nonik0/Light-Rail/images/github-qr.png

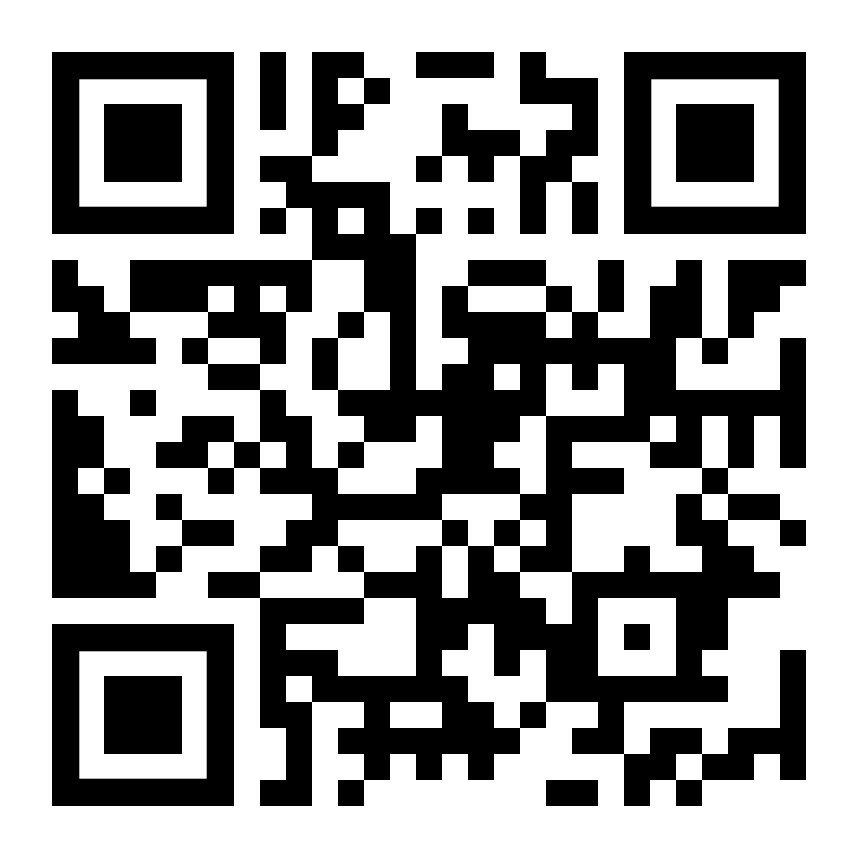
images/github-qr.png
