nonik0/Light-Rail/images/train_drawing_1.png

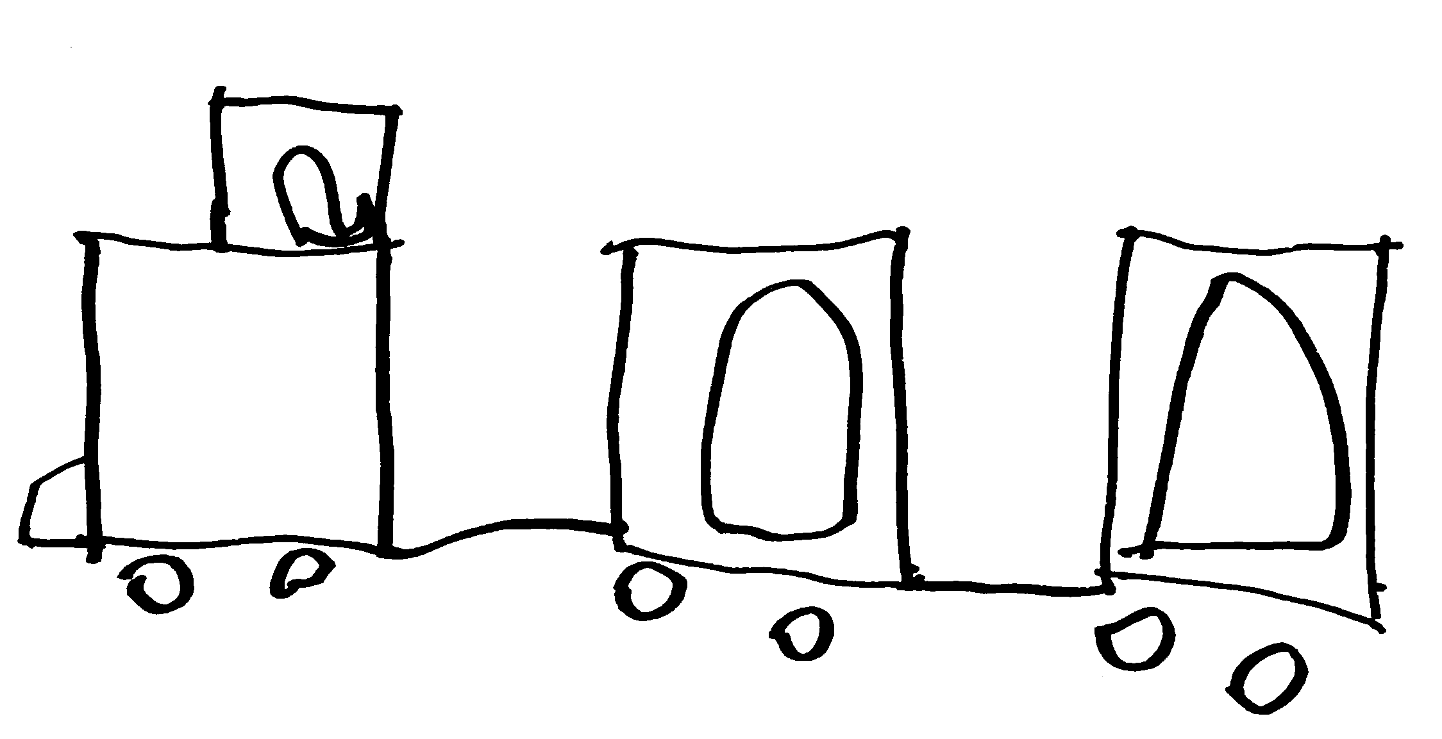
images/train_drawing_1.png
