nonik0/Light-Rail/images/train_drawing_2.png

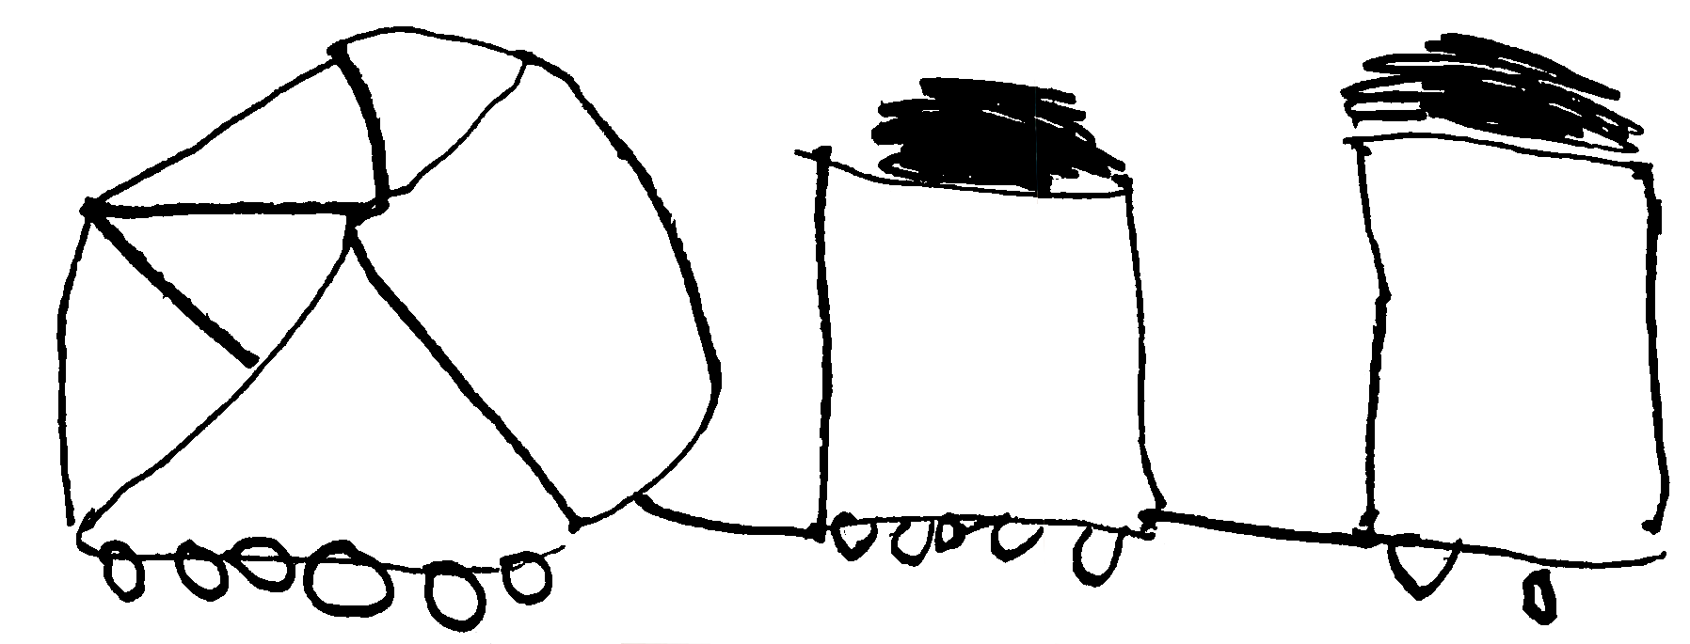
images/train_drawing_2.png
