nonik0/Light-Rail/firmware/rust/src/game_state.rs

use heapless::Vec;

use crate::{
    cargo::*,
    game_settings::GameSettings,
    location::{Direction, NUM_PLATFORMS, NUM_SWITCHES},
    platform::Platform,
    random::Rand,
    switch::Switch,
    train::{Car, Train, DEFAULT_SPEED},
    NUM_DIGITS,
};

pub const MAX_CARS: usize = 128;
pub const MAX_TRAINS: usize = 8;
pub const TRAIN_SIZE: usize = MAX_CARS / MAX_TRAINS;

#[derive(Clone, Copy, PartialEq)]
pub enum DisplayState {
    None,
    Score(u16),
    Segments([u8; NUM_DIGITS as usize]),
    Text([u8; NUM_DIGITS as usize]),
}

#[allow(dead_code)]
impl DisplayState {
    pub const DED: DisplayState = DisplayState::Text(*b"ded");
    pub const GG: DisplayState = DisplayState::Text(*b" gg");
    pub const OVR: DisplayState = DisplayState::Text(*b"ovr");
    pub const PAUSE_BYTES: [u8; NUM_DIGITS as usize] = [0u8, 0x36, 0u8];
    pub const PAUSE: DisplayState = DisplayState::Segments(Self::PAUSE_BYTES);
}

// TODO: move mutable stuff to methods and make stuff private?
pub struct GameState {
    pub target_mode_index: usize, // in state so menu mode can manipulate it
    // TODO: combine active/over/paused into single enum state
    pub is_over: bool,   // stops entity updates, game is over
    pub is_paused: bool, // stops entity updates, game is still active
    pub redraw: bool,    // flag to redraw board LEDs
    pub display: DisplayState,
    pub settings: GameSettings,

    // game entities
    pub cars: [Car; MAX_CARS],
    pub trains: Vec<Train, MAX_TRAINS>,
    pub platforms: [Platform; NUM_PLATFORMS],
    pub switches: [Switch; NUM_SWITCHES],
}

impl GameState {
    pub fn add_train(&mut self, cargo: Cargo, num_cars: u8, max_cars: u8, speed: Option<u8>) {
        if self.trains.is_full() {
            return;
        }

        // TODO: for now, simple allocation method that divides evenly on MAX_TRAINS, only snake allocated single train with max cars
        let cars_ptr = unsafe { self.cars.as_mut_ptr().add(self.trains.len() * TRAIN_SIZE) };
        let loc = self.rand_platform().track_location();
        let mut train = Train::new(cars_ptr, max_cars, loc, cargo, speed);
        for _ in 1..num_cars {
            train.add_car(cargo);
        }
        self.trains.push(train).ok();
        self.redraw = true;
    }

    #[allow(dead_code)]
    pub fn remove_train(&mut self) {
        if self.trains.len() > 1 {
            self.trains.pop();
            self.redraw = true;
        }
    }

    /// Initializes the game state with a single train with given parameters.
    pub fn init_trains(&mut self, cargo: Cargo, num_cars: u8, max_cars: u8) {
        // init first train
        if self.trains.len() > 0 {
            while self.trains.len() > 1 {
                self.trains.pop();
            }

            // reuse existing train for smooth transition between modes
            let train = &mut self.trains[0];
            train.init_cars(cargo, num_cars, max_cars);
            train.set_speed(DEFAULT_SPEED);
            self.redraw = true;
        } else {
            self.add_train(cargo, num_cars, max_cars, None);
        }
    }

    pub fn init_platforms(&mut self, cargo: Cargo) {
        for platform in self.platforms.iter_mut() {
            if !platform.is_empty() {
                platform.set_cargo_out(cargo);
                platform.set_phase_speed(1);
            }
        }
    }

    pub fn clear_platforms(&mut self) {
        for platform in self.platforms.iter_mut() {
            platform.clear_cargo();
        }
    }

    pub fn rand_platform(&self) -> &Platform {
        let rand_platform_index = Rand::from_range(0, self.platforms.len() as u8 - 1) as usize;
        &self.platforms[rand_platform_index]
    }

    // Helper/utility functions for state

    /// If the train just left a switch, switch it.
    pub fn train_switch(&mut self, train_index: usize) {
        let train = &self.trains[train_index];
        let caboose_loc = train.caboose().loc;
        let last_loc = train.last_loc();

        // If train just left a switch, randomly switch it
        for switch in self.switches.iter_mut() {
            if caboose_loc == switch.location() {
                continue; // Train is entering, not leaving
            }
            for dir in [Direction::Anode, Direction::Cathode] {
                if switch.active_location(dir) == Some(last_loc) {
                    switch.switch();
                    break;
                }
            }
        }
    }

    /// True if the train can actually transfer with a given platform: either the
    /// platform wants cargo the train is carrying, or the platform is offering
    /// cargo and the train has room to take it.
    #[inline(always)]
    fn platform_transfer_possible(train: &Train, platform: &Platform) -> bool {
        if platform.is_empty() {
            return false;
        }

        let (platform_cargo, is_receiving) = platform.cargo();
        if is_receiving {
            train.has_cargo(platform_cargo)
        } else {
            !train.is_full()
        }
    }

    // True if train is within `steps` advances of a platform that has cargo the
    // train is actually able to pick up or drop off
    pub fn train_approaching_platform(&self, train_index: usize, steps: u8) -> bool {
        let train = &self.trains[train_index];
        let mut loc = train.front();
        let mut dir = train.direction();

        for _ in 0..steps {
            let is_switched = self
                .switches
                .iter()
                .any(|switch| loc == switch.location() && switch.is_switched(dir));
            let (next_loc, next_dir) = loc.next(dir, is_switched);
            loc = next_loc;
            dir = next_dir;
        }

        self.platforms.iter().any(|platform| {
            platform.track_location() == loc && Self::platform_transfer_possible(train, platform)
        })
    }

    /// True if a train's engine is at the last platform track, i.e. the train is fully "in position"
    /// in front of a set of adjacent platforms, and the train has cargo to pick up or drop off
    pub fn train_ready_at_platform(&self, train_index: usize) -> bool {
        let train = &self.trains[train_index];
        let engine_loc = train.front();
        let next_loc = train.next_loc(&self.switches);

        let mut engine_at_platform = false;
        let mut next_loc_at_platform = false;
        let mut any_ready = false;

        for platform in self.platforms.iter() {
            let loc = platform.track_location();

            if loc == engine_loc {
                engine_at_platform = true;
            }
            if loc == next_loc {
                next_loc_at_platform = true;
            }
            if train.at_location(loc) && Self::platform_transfer_possible(train, platform) {
                any_ready = true;
            }
        }

        engine_at_platform && !next_loc_at_platform && any_ready
    }
}
