nonik0/Light-Rail/firmware/rust/src/train.rs

use random_trait::Random;

use crate::{
    cargo::*,
    game_settings::GameSettings,
    location::{Direction, Location},
    random::Rand,
    switch::Switch,
};

pub const DEFAULT_SPEED: u8 = 10;
const MIN_SPEED: u8 = 0;
const MAX_SPEED: u8 = 100;

#[derive(Clone, Copy, Default)]
pub struct Car {
    pub loc: Location,
    pub cargo: Cargo,
    pub last_brightness: u8,
}

pub struct Train {
    direction: Direction,
    speed: u8,
    speed_counter: u8,
    cars_ptr: *mut Car,
    num_cars: u8,
    max_cars: u8,
    last_loc: Location,
    phase: u8, // phase of the train, used for PWM
}

impl Train {
    pub fn new(
        cars_ptr: *mut Car,
        max_cars: u8,
        loc: Location,
        cargo: Cargo,
        speed: Option<u8>,
    ) -> Self {
        let mut new_self = Self {
            direction: if Rand::default().get_bool() {
                Direction::Anode
            } else {
                Direction::Cathode
            },
            speed: speed.unwrap_or(DEFAULT_SPEED),
            speed_counter: 0,
            cars_ptr,
            num_cars: 0,
            max_cars,
            last_loc: loc,
            phase: Rand::default().get_u8(), // initial phase
        };

        new_self.add_car(cargo);
        new_self
    }

    pub fn add_car(&mut self, cargo: Cargo) -> Option<Location> {
        if self.num_cars >= self.max_cars {
            return None;
        }

        let loc = if self.num_cars == 0 {
            self.last_loc
        } else {
            let caboose_loc = self.caboose().loc;
            let inv_caboose_dir = if self.num_cars > 1 {
                let next_car_loc = self.cars()[self.num_cars as usize - 2].loc;
                if caboose_loc
                    .next(Direction::Anode, Rand::default().get_bool())
                    .0
                    == next_car_loc
                {
                    Direction::Cathode
                } else {
                    Direction::Anode
                }
            } else {
                self.direction
            };
            caboose_loc.next(inv_caboose_dir, false).0 // TODO: is switched
        };

        self.num_cars += 1;
        let new_car = self.cars_mut().last_mut().unwrap();
        new_car.loc = loc;
        new_car.cargo = cargo;

        Some(loc)
    }

    #[allow(dead_code)]
    pub fn remove_car(&mut self) -> Option<Location> {
        if self.num_cars <= 1 {
            return None;
        }

        let loc = self.caboose().loc;
        self.num_cars -= 1;
        Some(loc)
    }

    /// Unsafe function if not called properly, should only be called when first train is initialized
    pub fn init_cars(&mut self, cargo: Cargo, num_cars: u8, max_cars: u8) {
        self.num_cars = num_cars;
        self.max_cars = max_cars;

        for car in self.cars_mut().iter_mut() {
            car.cargo = cargo;
            car.last_brightness = 0;
        }
    }

    // Game tick for train during game over or pause, to keep led updates occuring
    pub fn update<F>(
        &mut self,
        settings: &GameSettings,
        mut update_callback: F,
        force_update: bool,
    )
    where
        F: FnMut(Location, u8),
    {
        self.phase = self.phase.wrapping_add(1);

        for car in self.cars_mut().iter_mut() {
            let brightness = car
                .cargo
                .car_brightness(self.phase, settings.car_brightness());
            if force_update || car.last_brightness != brightness {
                car.last_brightness = brightness;
                update_callback(car.loc, brightness);
            }
        }
    }

    /// Game tick for train, returns location updates as cars move along track
    pub fn advance<F>(
        &mut self,
        settings: &GameSettings,
        switches: &[Switch],
        mut update_callback: F,
        force_update: bool,
    ) -> bool
    where
        F: FnMut(Location, u8),
    {
        self.speed_counter += self.speed;

        // If not enough speed accumulated, just update brightness and return
        if self.speed_counter < MAX_SPEED {
            self.update(settings, update_callback, force_update);
            return false;
        }

        self.phase = self.phase.wrapping_add(1);
        self.speed_counter -= MAX_SPEED;

        // Move train cars from rear to front, updating locations and brightness
        self.last_loc = self.caboose().loc;
        update_callback(self.last_loc, 0);

        let cars = self.cars_mut();
        for i in (1..cars.len()).rev() {
            cars[i].loc = cars[i - 1].loc;
            let brightness = cars[i]
                .cargo
                .car_brightness(self.phase, settings.car_brightness());
            update_callback(cars[i].loc, brightness);
        }

        // Advance the engine to the next location and update brightness
        let (next_loc, new_dir) = self.next(switches);
        self.engine_mut().loc = next_loc;
        self.direction = new_dir;
        let brightness = self
            .engine()
            .cargo
            .car_brightness(self.phase, settings.car_brightness());
        update_callback(self.front(), brightness);

        true
    }

    // Returns the train engine's next location
    pub fn next_loc(&self, switches: &[Switch]) -> Location {
        let (loc, _) = self.next(switches);
        loc
    }

    /// Returns the train engine's next location and direction
    pub fn next(&self, switches: &[Switch]) -> (Location, Direction) {
        // Determine if the front of the train is on a switched track
        let front_loc = self.front();
        let is_switched = switches
            .iter()
            .any(|switch| front_loc == switch.location() && switch.is_switched(self.direction));

        // Get next location and direction
        self.front().next(self.direction, is_switched)
    }

    /// Returns the vector of cars in the train
    pub fn cars(&self) -> &[Car] {
        unsafe { core::slice::from_raw_parts(self.cars_ptr, self.num_cars as usize) }
    }

    /// Returns the number of cars in the train
    pub fn len(&self) -> usize {
        self.num_cars as usize
    }

    /// Returns speed of the train
    pub fn speed(&self) -> u8 {
        self.speed
    }

    /// Sets the speed of the train, clamping it between MIN_SPEED and MAX_SPEED
    pub fn set_speed(&mut self, speed: u8) {
        self.speed = speed.clamp(MIN_SPEED, MAX_SPEED);
        self.speed_counter = 0;
    }

    /// Advances speed counter so train advances next tick
    pub fn force_advance_next_tick(&mut self) {
        self.speed_counter = MAX_SPEED;
    }

    // Returns true if the train has a car with cargo
    pub fn has_cargo(&self, cargo: Cargo) -> bool {
        self.cars().iter().any(|car| car.cargo == cargo)
    }

    /// Returns true if every car is currently carrying cargo
    pub fn is_full(&self) -> bool {
        self.cars().iter().all(|car| car.cargo != Cargo::Empty)
    }

    /// Adds cargo to train, returns true if train loads cargo into an available empty car
    /// TODO: add location so cargo can be added to nearest empty car?
    pub fn load_cargo(&mut self, cargo: Cargo) -> bool {
        match self.cars_mut().iter_mut().find(|car| car.cargo == Cargo::Empty) {
            Some(car) => {
                car.cargo = cargo;
                true
            }
            None => false,
        }
    }

    /// Unloads cargo from the train, returns true if train removes cargo from a car that has it
    pub fn unload_cargo(&mut self, cargo: Cargo) -> bool {
        match self.cars_mut().iter_mut().find(|car| car.cargo == cargo) {
            Some(car) => {
                car.cargo = Cargo::Empty;
                true
            }
            None => false,
        }
    }


    /// Returns reference to the first car of the train (engine)
    pub fn engine(&self) -> &Car {
        self.cars().first().unwrap()
    }

    /// Returns the current location of the train engine
    pub fn front(&self) -> Location {
        self.engine().loc
    }

    /// Returns reference to the last car of the train (caboose)
    pub fn caboose(&self) -> &Car {
        self.cars().last().unwrap()
    }

    /// Returns the direction of the train
    pub fn direction(&self) -> Direction {
        self.direction
    }

    /// Returns the previous location of the caboose before the last move
    pub fn last_loc(&self) -> Location {
        self.last_loc
    }

    /// Returns bool if any car is at the given location
    pub fn at_location(&self, loc: Location) -> bool {
        self.cars().iter().any(|car| car.loc == loc)
    }

    // private mutable functions

    /// Returns mutable reference to the engine (first car of the train)
    fn engine_mut(&mut self) -> &mut Car {
        self.cars_mut().first_mut().unwrap()
    }

    // /// Returns mutable reference to the last car of the train (caboose)
    // fn caboose_mut(&mut self) -> &mut Car {
    //     self.cars_mut().last_mut().unwrap()
    // }

    /// Returns the vector of cars in the train
    fn cars_mut(&self) -> &mut [Car] {
        unsafe { core::slice::from_raw_parts_mut(self.cars_ptr, self.num_cars as usize) }
    }
}

impl core::ops::Index<usize> for Train {
    type Output = Car;

    fn index(&self, index: usize) -> &Self::Output {
        &self.cars()[index]
    }
}
