nonik0/Light-Rail/firmware/cpp/track.h

#pragma once

#include <Arduino.h>

#define TRACK_COUNT 144
#define TRACK_NONE 0xFF

struct Track
{
  // defined "backwards" because AVR is little-endian
  uint8_t cathodeNextLoc2; // neighbor2 on cathode side
  uint8_t anodeNextLoc2;   // neighbor2 on anode side
  uint8_t cathodeNextLoc;  // neighbor on cathode side
  uint8_t anodeNextLoc;    // neighbor on anode side
};

#ifndef LED_BACKPACK_MATRIX
const uint32_t TrackData[TRACK_COUNT] = {
    0x6111FFFF, // track 0/0x00
    0x20202020, // track 1/0x01 PLATFORM
    0x3003FFFF, // track 2/0x02
    0x7002FFFF, // track 3/0x03
    0x5082FFFF, // track 4/0x04
    0x60606060, // track 5/0x05 PLATFORM
    0x70707070, // track 6/0x06 PLATFORM
    0x8042FFFF, // track 7/0x07
    0x0D69FF1D, // track 8/0x08
    0x682DFFFF, // track 9/0x09
    0x4838FFFF, // track 10/0x0A
    0x3B5CFFFF, // track 11/0x0B
    0x1839FFFF, // track 12/0x0C
    0x0868FFFF, // track 13/0x0D
    0x4C4EFFFF, // track 14/0x0E
    0x88888888, // track 15/0x0F PLATFORM
    0x4920FFFF, // track 16/0x10
    0x0021FFFF, // track 17/0x11
    0x2933FFFF, // track 18/0x12
    0x53535353, // track 19/0x13 PLATFORM
    0x5154FFFF, // track 20/0x14
    0x61616161, // track 21/0x15 PLATFORM
    0x5351FFFF, // track 22/0x16
    0x1E81FFFF, // track 23/0x17
    0x4F0CFFFF, // track 24/0x18
    0x594AFFFF, // track 25/0x19
    0x39393939, // track 26/0x1A PLATFORM
    0x6949FFFF, // track 27/0x1B
    0x59595959, // track 28/0x1C PLATFORM
    0x0848FFFF, // track 29/0x1D
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
    0x8789FFFF, // track 136/0x88
    0x888AFFFF, // track 137/0x89
    0x898BFFFF, // track 138/0x8A
    0x8A8CFFFF, // track 139/0x8B
    0x8B8DFFFF, // track 140/0x8C
    0x8C8EFFFF, // track 141/0x8D
    0x8D8FFFFF, // track 142/0x8E
    0x8E7FFFFF, // track 143/0x8F
};
#endif
