nonik0/Light-Rail/firmware/rust/src/game.rs

use as1115::AS1115;
use embedded_hal::i2c::I2c;
use heapless::Vec;
use is31fl3731::{gamma, IS31FL3731};

use crate::{
    game_settings::GameSettings,
    game_state::*,
    input::{BoardInput, InputDirection, InputEvent},
    location::Location,
    modes::*,
    platform::Platform,
    switch::Switch,
    tone::TimerTone,
    train::{Car, Train},
    NUM_DIGITS,
};

pub struct Game<I2C>
where
    I2C: I2c,
{
    // board components
    board_buzzer: TimerTone,
    board_digits: AS1115<I2C, NUM_DIGITS>,
    board_input: BoardInput,
    board_leds: IS31FL3731<I2C>,

    // game mode state
    mode_index: usize,
    mode: GameMode,
    last_display: DisplayState,

    // state passed to game modes, changes to state entities are rendered into updates for digits and LEDs
    state: GameState,
}

impl<I2C> Game<I2C>
where
    I2C: I2c,
{
    pub fn new(
        board_buzzer: TimerTone,
        board_digits: AS1115<I2C, NUM_DIGITS>,
        board_input: BoardInput,
        board_leds: IS31FL3731<I2C>,
        cars: [Car; MAX_CARS],
        settings: GameSettings,
    ) -> Self {
        let platforms = Platform::take();
        let switches = Switch::take();
        let trains = Vec::<Train, MAX_TRAINS>::new();

        let state = GameState {
            target_mode_index: 0,
            is_paused: false,
            is_over: false,
            redraw: false,
            display: DisplayState::None,
            settings,
            cars,
            trains,
            platforms,
            switches,
        };

        Self {
            board_buzzer,
            board_digits,
            board_input,
            board_leds,
            mode_index: 0,
            mode: GameMode::default(),
            last_display: DisplayState::None,
            state,
        }
    }

    pub fn base_delay(&self) -> u32 {
        self.state.settings.game_speed() as u32
    }

    pub fn restart(&mut self) {
        self.board_digits.display_value(1).ok();
        self.mode = GameMode::from_index(self.mode_index);
        self.mode.on_restart(&mut self.state);
        self.state.redraw = true;
    }

    pub fn tick(&mut self) {
        // handle input events, some events are shared betweens all modes
        if let Some(event) = self.board_input.update() {
            match event {
                // toggle switches
                InputEvent::SwitchButtonPressed(index) => {
                    if self.state.settings.is_buzzer_enabled() {
                        self.board_buzzer.tone(3000, 15);
                    }
                    let index = index as usize;
                    if index < self.state.switches.len() {
                        self.state.switches[index].switch();
                    }
                }
                // tones on button presses
                InputEvent::DirectionButtonPressed(InputDirection::Up)
                | InputEvent::DirectionButtonPressed(InputDirection::Right) => {
                    if self.state.settings.is_buzzer_enabled() {
                        self.board_buzzer.tone(3500, 10);
                    }
                }
                InputEvent::DirectionButtonPressed(InputDirection::Down)
                | InputEvent::DirectionButtonPressed(InputDirection::Left) => {
                    if self.state.settings.is_buzzer_enabled() {
                        self.board_buzzer.tone(3000, 10);
                    }
                }
                // exit to menu mode
                InputEvent::DirectionButtonHeld(InputDirection::Up)
                | InputEvent::DirectionButtonHeld(InputDirection::Down) => {
                    if self.state.settings.is_buzzer_enabled() {
                        self.board_buzzer.tone(3000, 10);
                    }
                    // save settings when exiting from settings mode
                    if matches!(self.mode, GameMode::SettingsMode(_)) {
                        self.state.settings.save();
                    }
                    self.state.target_mode_index = 0;
                    self.mode_index = 0;
                    self.state.is_over = false;
                    self.state.is_paused = false;
                    self.restart();
                    //return;
                }
                _ => {}
            }

            self.mode.on_input_event(event, &mut self.state);
        }

        // change mode when current mode requests it (mostly from menu mode)
        if self.state.target_mode_index != self.mode_index {
            self.mode_index = self.state.target_mode_index;
            self.restart();
        }

        self.mode.on_game_tick(&mut self.state);

        // update board digits/score display
        if self.last_display != self.state.display {
            self.last_display = self.state.display;

            // TODO: flag or something to avoid calling unnecessarily
            self.board_digits
                .set_intensity(self.state.settings.digit_brightness_level())
                .ok();

            match self.state.display {
                DisplayState::None => {
                    self.board_digits.clear().ok();
                }
                DisplayState::Score(score) => {
                    self.board_digits.display_value(score).ok();
                }
                DisplayState::Segments(ref segments) => {
                    self.board_digits.display_segments(segments).ok();
                }
                DisplayState::Text(ref text) => {
                    self.board_digits.display_ascii(text).ok();
                }
            }
        }

        // clear board LEDs and force update all entities when requested
        if self.state.redraw {
            self.board_leds.clear_blocking().ok();
        }

        // helper closure to update entity LEDs
        let mut do_led_update = |location: Location, brightness: u8| {
            self.board_leds
                .pixel_blocking(location.index(), gamma(brightness))
                .ok();
        };

        // update train entities
        let mut event_indices = heapless::Vec::<usize, MAX_TRAINS>::new();
        for (train_index, train) in self.state.trains.iter_mut().enumerate() {
            // skip updating game entities if game is paused or over
            // just update train rather than advance if game over or paused
            if self.state.is_over || self.state.is_paused {
                train.update(&self.state.settings, &mut do_led_update, self.state.redraw);
            } else {
                if train.advance(
                    &self.state.settings,
                    &self.state.switches,
                    &mut do_led_update,
                    self.state.redraw,
                ) {
                    event_indices.push(train_index).ok();
                }
            }
        }

        // call advance callbacks for any trains that moved
        for &train_index in event_indices.iter() {
            self.mode.on_train_advance(train_index, &mut self.state);
        }

        // update platform and switches entities
        for platform in self.state.platforms.iter_mut() {
            platform.update(&self.state.settings, &mut do_led_update, self.state.redraw);
        }
        for switch in self.state.switches.iter_mut() {
            switch.update(
                &self.state.settings,
                &self.state.trains,
                &mut do_led_update,
                self.state.redraw,
            );
        }

        self.state.redraw = false;
    }
}
